ervanalb/lux/hub_firmware/src/main.c

#include "hal.h"
#include "usbd_cdc_core.h"
#include  "usbd_usr.h"

USB_CORE_HANDLE  USB_Device_dev ;

int main()
{
    init();
    set_enabled_channels(0x3F);
    enable_rx();
    USBD_Init(&USB_Device_dev,
              &USR_desc, 
              &USBD_CDC_cb, 
              &USR_cb);

    for(;;);
}
