ervanalb/lux/liblux/embedded/lux.c

#include <string.h>
#include "lux.h"

#include "lux_hal.h"

// Global variables

// Flag indicating whether there is currently a received packet in lux_packet
uint8_t lux_packet_in_memory;
// Global lux packet
struct lux_packet lux_packet;
// Global lux packet counters
struct lux_counters lux_counters;

// Local variables

// The current state of the encoder / decoder (codec)
static enum
{
    CODEC_START,
    READ_DESTINATION,
    READ_COMMAND,
    READ_INDEX,
    READ_PAYLOAD,
    SKIP_CURRENT_PACKET,
    ENCODE,
    ENCODER_STALLED,
} codec_state;

// The current sub-state of the encoder (within ENCODE / ENCODER_STALLED)
static enum
{
    ENCODER_START,
    WRITE_DESTINATION,
    WRITE_COMMAND,
    WRITE_INDEX,
    WRITE_PAYLOAD,
    WRITE_CRC,
    FLUSH,
} encoder_state;

// Pointer to current index in lux_packet.payload
static int16_t packet_pointer;
// Pointer to current index in lux_packet.destination
static int8_t destination_pointer;
// Temporary home for destination until we can be sure it matches
static uint8_t tmp_destination[LUX_DESTINATION_SIZE];

// Number of bytes remaining in the COBS block
static uint8_t cobs_remaining;
// Flag indicating whether or not a zero byte is due at the end of this COBS block
static uint8_t cobs_add_zero;

// Buffer and pointers for the COBS encoder to hold the current block
static uint8_t cobs_encoder_fill_ptr;
static uint8_t cobs_encoder_send_ptr;
static uint8_t cobs_buffer[256];

// Local functions

// Prepare COBS decoder for the start of a new block
static void reset_cobs_decoder()
{
    cobs_remaining=0;
    cobs_add_zero=0;
}

// Decode one COBS byte from src, and put the result in *dest
// Returns 1 if *dest was populated, 0 otherwise.
static uint8_t cobs_decode(uint8_t src, uint8_t* dest)
{
    uint8_t result;
    if(!cobs_remaining)
    {
        cobs_remaining=src-1;
        result=cobs_add_zero;
        if(cobs_add_zero)
        {
            lux_hal_crc(0);
            *dest=0;
        }
        cobs_add_zero = (src < 255);
        return result;
    }

    cobs_remaining--;
    lux_hal_crc(src);
    *dest=src;
    return 1;
}

// Prepare the COBS encoder for the start of a new block
static void reset_cobs_encoder()
{
    cobs_encoder_fill_ptr=1;
}

// Write out as much of the remaining bytes in the COBS encoder buffer as possible.
// Returns 1 if the message was completely transmitted.
static uint8_t write_continuation()
{
    while(cobs_encoder_send_ptr<cobs_encoder_fill_ptr && lux_hal_bytes_to_write())
    {
        lux_hal_write_byte(cobs_buffer[cobs_encoder_send_ptr++]);
    }

    if(cobs_encoder_send_ptr == cobs_encoder_fill_ptr)
    {
        reset_cobs_encoder();
        return 1;
    }
    return 0;
}

// Write out the current COBS encoder buffer.
// Returns 1 if the message was completely transmitted.
// If the message was not completely transmitted, subsequent calls to
// write_continuation are necessary before additional COBS encoding
// can be performed.
static uint8_t write()
{
    cobs_encoder_send_ptr=0;
    return write_continuation();
}

// Encode a byte using COBS and send it (buffered by block.)
// Returns 1 if additional bytes can be written.
// If this function returns 0, subsequent calls to
// write_continuation are necessary before additional COBS encoding
// can be performed.
static uint8_t cobs_encode_and_send(uint8_t byte)
{
    lux_hal_crc(byte);

    if(byte == 0) goto write;

    cobs_buffer[cobs_encoder_fill_ptr++] = byte;

    if(cobs_encoder_fill_ptr == 255) goto write;

    return 1;

    write:
    cobs_buffer[0] = cobs_encoder_fill_ptr;
    return write();
}

// Finishes the current COBS block, adds a null terminator, and writes it out.
// Returns 1 if the message was completely transmitted.
// If the message was not completely transmitted, subsequent calls to
// write_continuation are necessary before additional COBS encoding
// can be performed.
static uint8_t cobs_encode_flush()
{
    cobs_buffer[0] = cobs_encoder_fill_ptr;
    cobs_buffer[cobs_encoder_fill_ptr++] = 0;
    return write();
}

// Global functions

void lux_init()
{
    lux_reset_counters();
    lux_hal_enable_rx();

    codec_state=CODEC_START;
}

// Do any necessary work to handle incoming or outgoing data
// Calls lux_fn_rx() when a packet has arrived.
// Call this repeatedly in your application's main loop.
void lux_codec()
{
    uint8_t byte_read;
    uint8_t decoded_byte;

    switch(codec_state)
    {
        case CODEC_START:
        read_destination:
            codec_state=READ_DESTINATION;
            destination_pointer=0;
            lux_hal_reset_crc();
            reset_cobs_decoder();
        case READ_DESTINATION:
            while(lux_hal_bytes_to_read())
            {
                byte_read=lux_hal_read_byte();
                if(!byte_read) goto read_destination; // Don't bother incrementing any counters because this is probably noise
                if(cobs_decode(byte_read,&decoded_byte))
                {
                    tmp_destination[destination_pointer++]=decoded_byte;
                }
                if(destination_pointer == LUX_DESTINATION_SIZE)
                {
                    uint32_t destination;
                    memcpy(&destination, tmp_destination, sizeof(destination));
                    if(lux_fn_match_destination(destination))
                    {
                        if(lux_packet_in_memory)
                        {
                            lux_counters.packet_overrun++;
                            goto skip_current_packet;
                        }
                        else
                        {
                            lux_packet.destination = destination;
                            goto read_command;
                        }
                    }
                    lux_counters.bad_address++;
                    goto skip_current_packet;
                }
            }
            break;

        read_command:
        codec_state = READ_COMMAND;
        case READ_COMMAND:
            while(lux_hal_bytes_to_read())
            {
                byte_read = lux_hal_read_byte();
                if (!byte_read)
                {
                    lux_counters.malformed_packet++;
                    goto read_destination;
                }
                if (cobs_decode(byte_read, &decoded_byte))
                {
                    lux_packet.command = decoded_byte;
                    goto read_index;
                }
            }
            break;

        read_index:
        codec_state = READ_INDEX;
        case READ_INDEX:
            while(lux_hal_bytes_to_read())
            {
                byte_read = lux_hal_read_byte();
                if (!byte_read)
                {
                    lux_counters.malformed_packet++;
                    goto read_destination;
                }
                if (cobs_decode(byte_read, &decoded_byte))
                {
                    lux_packet.index = decoded_byte;
                    goto read_payload;
                }
            }
            break;

        read_payload:
        codec_state=READ_PAYLOAD;
        packet_pointer=0;
        case READ_PAYLOAD:
            while(lux_hal_bytes_to_read())
            {
                byte_read=lux_hal_read_byte();
                if(!byte_read)
                {
                    if(lux_hal_crc_ok())
                    {
                        lux_packet.payload_length=packet_pointer-LUX_CRC_SIZE;
                        memcpy(lux_packet.crc, lux_packet.payload + lux_packet.payload_length, sizeof(lux_packet.crc));
                        lux_packet_in_memory=1;
                        lux_counters.good_packet++;
                        lux_fn_rx();
                        if(codec_state == ENCODE) goto encode;
                        goto read_destination;
                    }
                    lux_counters.bad_checksum++;
                    goto read_destination;
                }
                if(cobs_decode(byte_read,&decoded_byte))
                {
                    if(packet_pointer < LUX_PACKET_MEMORY_ALLOCATED_SIZE)
                    {
                        lux_packet.payload[packet_pointer++]=decoded_byte;
                    }
                    else
                    {
                        lux_counters.malformed_packet++;
                        goto skip_current_packet;
                    }
                }
            }
            break;
        skip_current_packet:
        codec_state=SKIP_CURRENT_PACKET;
        case SKIP_CURRENT_PACKET:
            while(lux_hal_bytes_to_read())
            {
                if(!lux_hal_read_byte()) goto read_destination;
            }
            break;

        encode:
        codec_state=ENCODE;
        case ENCODE:
            switch(encoder_state)
            {
                case ENCODER_START:
                    destination_pointer=0;
                    reset_cobs_encoder();
                    lux_hal_reset_crc();
                    encoder_state=WRITE_DESTINATION;
                case WRITE_DESTINATION:
                    while(destination_pointer<LUX_DESTINATION_SIZE)
                    {
                        uint8_t d;
                        memcpy(&d, ((uint8_t*) &lux_packet.destination) + destination_pointer++, 1);
                        if(!cobs_encode_and_send(d)) goto encoder_stalled;
                    }
                    encoder_state=WRITE_COMMAND;
                case WRITE_COMMAND:
                    if(!cobs_encode_and_send(lux_packet.command)) goto encoder_stalled;
                    encoder_state = WRITE_INDEX;
                case WRITE_INDEX:
                    if(!cobs_encode_and_send(lux_packet.index)) goto encoder_stalled;
                    encoder_state = WRITE_PAYLOAD;
                    packet_pointer = 0;
                case WRITE_PAYLOAD:
                    while(packet_pointer<lux_packet.payload_length)
                    {
                        if(!cobs_encode_and_send(lux_packet.payload[packet_pointer++])) goto encoder_stalled;
                    }
                    lux_hal_write_crc(&lux_packet.payload[packet_pointer]);
                    encoder_state=WRITE_CRC;
                case WRITE_CRC:
                    while(packet_pointer<lux_packet.payload_length+LUX_CRC_SIZE)
                    {
                        if(!cobs_encode_and_send(lux_packet.payload[packet_pointer++])) goto encoder_stalled;
                    }
                    encoder_state=FLUSH;
                    if(!cobs_encode_flush()) goto encoder_stalled; // Flush COBS
                case FLUSH:
                    if(lux_hal_tx_flush())
                    {
                        lux_hal_disable_tx();
                        lux_hal_enable_rx();
                        goto read_destination;
                    }
            }
            break;

        // XXX What is this for???
        encoder_stalled:
        codec_state = ENCODER_STALLED;
        case ENCODER_STALLED:
            if(write_continuation()) goto encode;
            break;
    }
}

// Call this function before altering lux_packet or lux_destination
void lux_stop_rx()
{
    if(lux_hal_bytes_to_read())
    {
        lux_counters.rx_interrupted++;
    }
    lux_hal_disable_rx();
}

// Output the packet stored in lux_packet to lux_destination and re-enable the receiver
void lux_start_tx()
{
    // Busywait: wait for RTS to go low
    codec_state=ENCODE;
    encoder_state=ENCODER_START;
    lux_hal_enable_tx();
}

// Reset all of the good/bad packet counters to zero
void lux_reset_counters(){
    memset(&lux_counters, 0, sizeof(lux_counters));
}
