ervanalb/lux/led_strip_firmware/app/inc/strip.h

#ifndef __STRIP_H
#define __STRIP_H

#include <stdint.h>
#include <config.h>

#define MAX_STRIP_LENGTH 340

void strip_init();
void strip_write(uint8_t* rgb_data, uint16_t length, uint16_t offset);
void strip_flush();
uint8_t strip_ready();

#endif
